tooyipjee/FLORA/images/DSCF9834.JPG

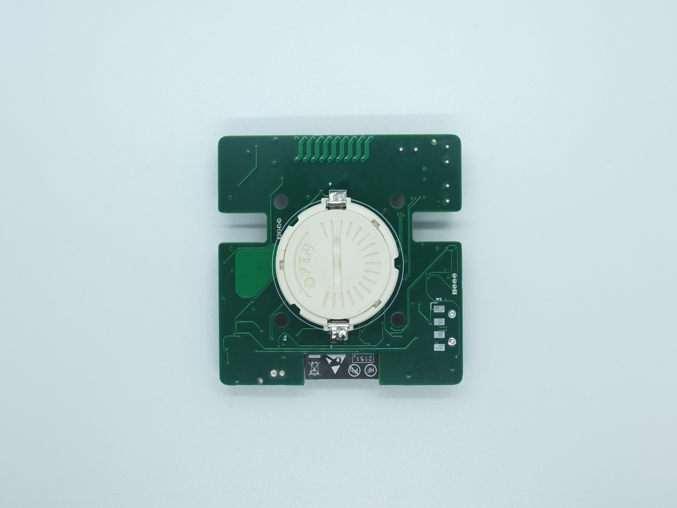
images/DSCF9834.JPG
